aluiziotomazelli/smart-farm-solar-sensor/docs/kicad/solar-sensor.kicad_sch

## KiCad design docs/kicad/solar-sensor.kicad_sch (2026-08-28)

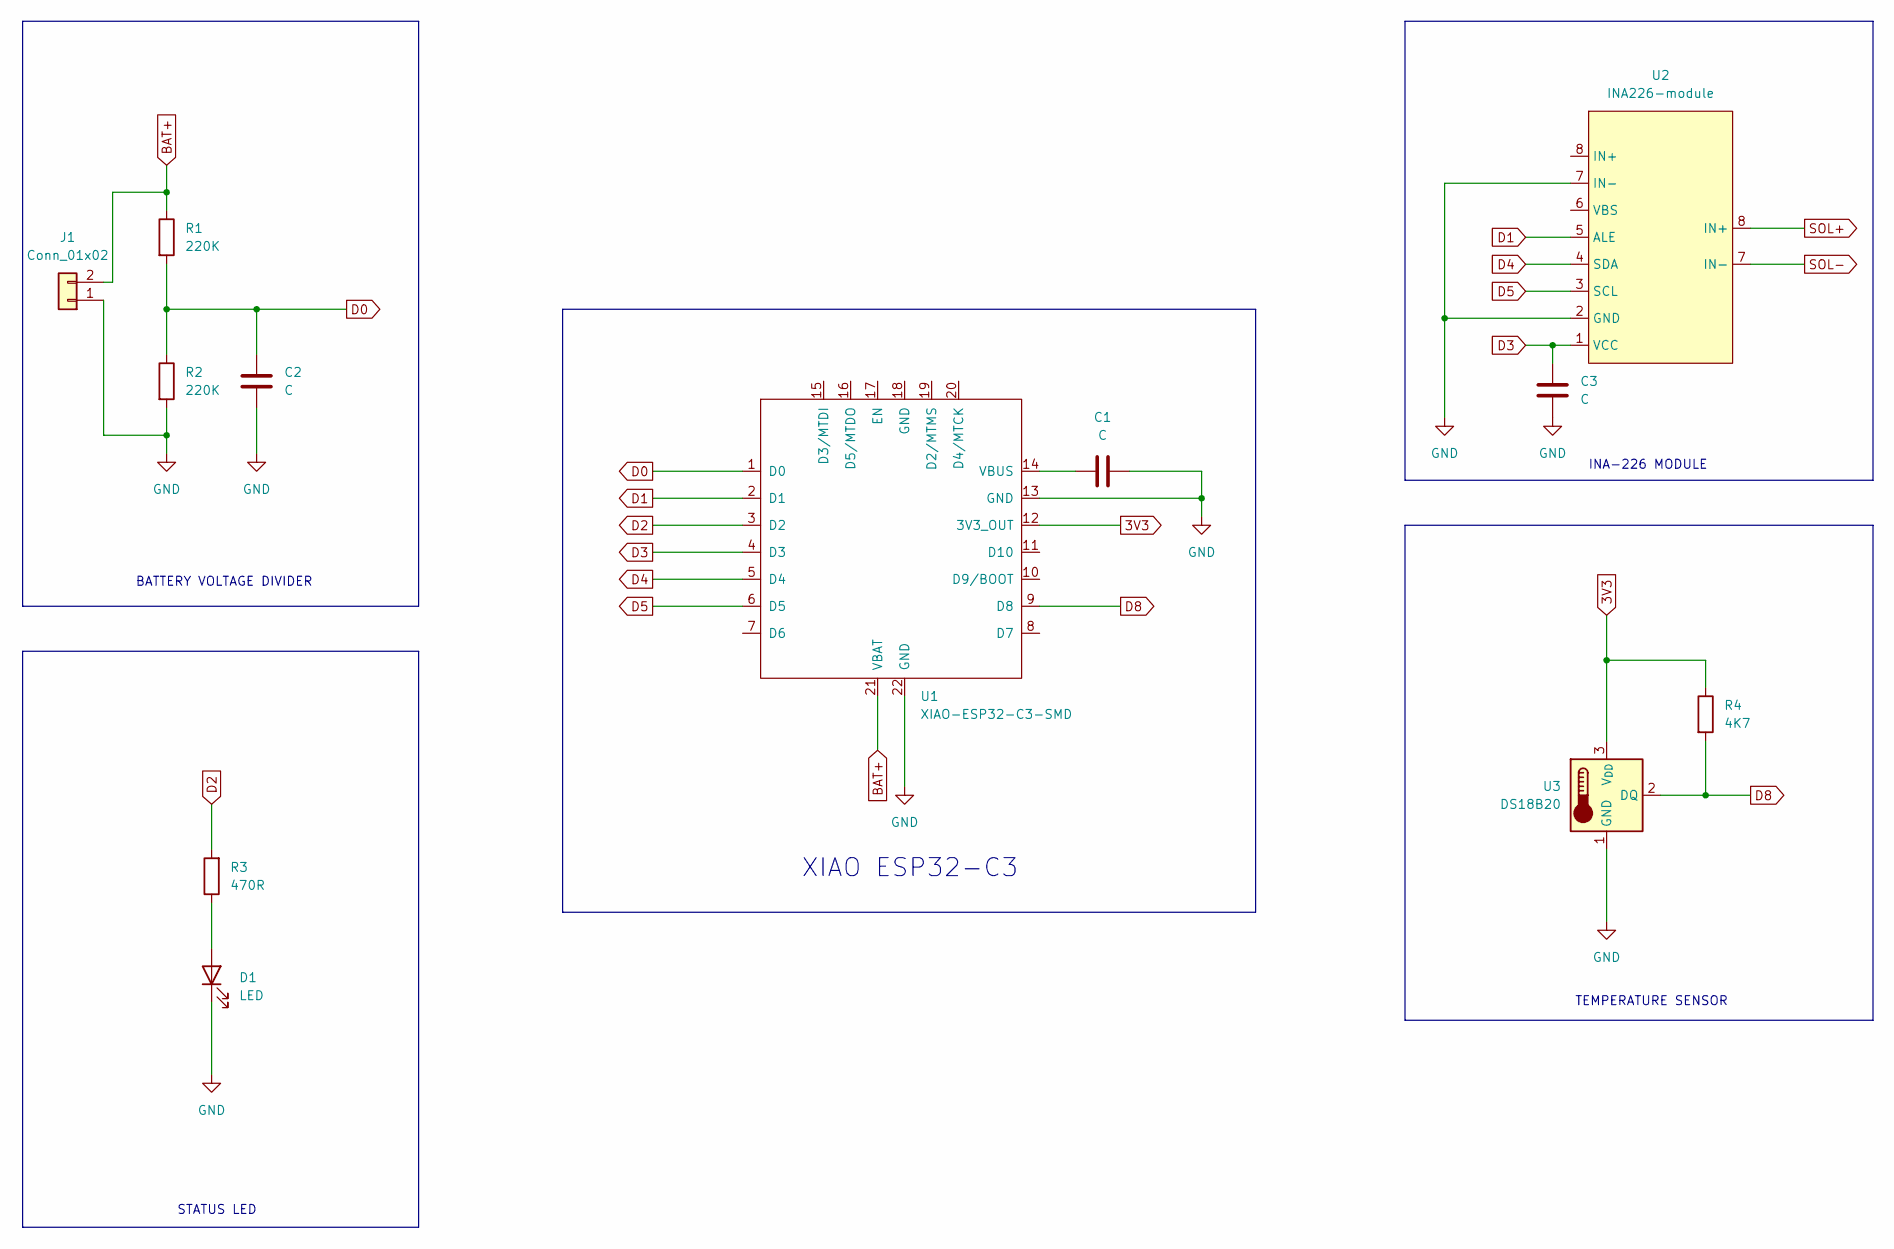
[picture p2: schematic solar-sensor.kicad_sch]

Parts:
C1, C2, C3: C; C_1206_3216Metric_Pad1.33x1.80mm_HandSolder
D1: LED; JST_EH_B2B-EH-A_1x02_P2.50mm_Vertical
J1: Conn_01x02; JST_EH_B2B-EH-A_1x02_P2.50mm_Vertical
R1, R2: 220K; R_1206_3216Metric_Pad1.30x1.75mm_HandSolder
R3: 470R; R_1206_3216Metric_Pad1.30x1.75mm_HandSolder
R4: 4K7; R_1206_3216Metric_Pad1.30x1.75mm_HandSolder
U1: XIAO-ESP32-C3-SMD
U2: INA226-module; PinSocket_1x08_P2.54mm_Vertical
U3: DS18B20; JST_EH_B3B-EH-A_1x03_P2.50mm_Vertical

Connections:
3V3: R4.1, U1.12 (3V3_OUT), U3.3 (V_{DD})
BAT+: J1.2, R1.1, U1.21 (VBAT)
D0: C2.2, R1.2, R2.1, U1.1 (D0)
D1: U1.2 (D1), U2.5 (ALE)
D2: R3.2, U1.3 (D2)
D3: C3.2, U1.4 (D3), U2.1 (VCC)
D4: U1.5 (D4), U2.4 (SDA)
D5: U1.6 (D5), U2.3 (SCL)
D8: R4.2, U1.9 (D8), U3.2 (DQ)
GND: C1.2, C2.1, C3.1, D1.1 (K), J1.1, R2.2, U1.13 (GND), U1.22 (GND), U2.2 (GND), U2.7 (IN-), U3.1 (GND)
unnamed: C1.1, U1.14 (VBUS)
unnamed: D1.2 (A), R3.1
SOL+: U2.8 (IN+)
SOL-: U2.7 (IN-)

Notes on the sheet:
BATTERY VOLTAGE DIVIDER
INA-226 MODULE
TEMPERATURE SENSOR
STATUS LED
XIAO ESP32-C3
