aluiziotomazelli/smart-farm-solar-sensor/host_test/test_solar_sensor/main/test_solar_sensor.cpp

#include <gtest/gtest.h>
#include <gmock/gmock.h>
#include <memory>

#include "solar_sensor.hpp"
#include "mock_ina_sensor_task.hpp"
#include "mock_slow_sensors_task.hpp"
#include "mocks/mock_espnow_manager.hpp"
#include "mock_time_manager.hpp"
#include "mock_persistence_backend.hpp"
#include "nvs_core.hpp"
#include "solar_sensor_nvs.hpp"

#include "mock_hal_timer.hpp"
#include "mock_hal_sleep.hpp"
#include "mock_hal_system.hpp"
#include "mock_hal_freertos.hpp"
#include "mock_hal_gpio.hpp"
#include "mock_hal_i2c.hpp"
#include "mock_ota_controller.hpp"
#include "mock_led_controller.hpp"
#include "mocks/mock_i_wifi_manager.hpp"
#include "mock_day_night_controller.hpp"
#include "mock_command_handler.hpp"

using ::testing::_;
using ::testing::DoAll;
using ::testing::NiceMock;
using ::testing::Return;
using ::testing::SetArgReferee;

class MockOtaTrigger : public IOtaTrigger
{
public:
    MOCK_METHOD(esp_err_t, arm, (IOtaTriggerListener& listener), (override));
    MOCK_METHOD(void, disarm, (), (override));
    MOCK_METHOD(void, notify, (), (override));
};

class SolarSensorTest : public ::testing::Test
{
protected:
    NiceMock<ina::MockInaSensorTask> mock_ina_task_;
    QueueHandle_t dummy_queue_ = reinterpret_cast<QueueHandle_t>(0x5678);
    TelemetrySnapshot snapshot_;
    NiceMock<MockSlowSensorsTask> mock_slow_sensors_task_;

    NiceMock<MockPersistenceBackend> rtc_core_backend_;
    NiceMock<MockPersistenceBackend> nvs_core_backend_;
    NvsCore core_storage_{rtc_core_backend_, nvs_core_backend_};

    NiceMock<MockPersistenceBackend> rtc_solar_backend_;
    NiceMock<MockPersistenceBackend> nvs_solar_backend_;
    SolarSensorNvs solar_storage_{rtc_solar_backend_, nvs_solar_backend_};

    NiceMock<idf_hals::MockTimerHAL> hal_timer_;
    NiceMock<MockOtaController> ota_controller_;
    NiceMock<MockOtaTrigger> btn_trigger_;
    NiceMock<espnow::MockEspNowManager> espnow_;
    QueueHandle_t rx_queue_ = reinterpret_cast<QueueHandle_t>(0x9999);
    NiceMock<wifi_manager::MockWiFiManager> wifi_;
    NiceMock<idf_hals::MockSleepHAL> hal_sleep_;
    NiceMock<idf_hals::MockSystemHAL> hal_system_;
    NiceMock<time_manager::MockTimeManager> time_manager_;
    NiceMock<idf_hals::MockHalFreertos> hal_rtos_;
    NiceMock<idf_hals::MockGpioHAL> hal_gpio_;
    NiceMock<idf_hals::MockI2cHAL> hal_i2c_;
    NiceMock<MockLedController> led_;
    NiceMock<MockDayNightController> day_night_;
    NiceMock<MockCommandHandler> command_handler_;

    class TestableSolarSensor : public SolarSensor
    {
    public:
        using SolarSensor::SolarSensor;
        using SolarSensor::ensure_communication_ready;
    };

    std::unique_ptr<TestableSolarSensor> sut_;

    uint64_t fake_time_us_ = 1000ULL;

    void SetUp() override
    {
        fake_time_us_ = 1000ULL;
        rtc_core_backend_.UseRealStorage();
        nvs_core_backend_.UseRealStorage();
        rtc_solar_backend_.UseRealStorage();
        nvs_solar_backend_.UseRealStorage();

        ON_CALL(hal_timer_, get_time_us()).WillByDefault(::testing::Invoke([this]() {
            uint64_t ret = fake_time_us_;
            fake_time_us_ += 50000ULL; // Advance 50ms per call
            return ret;
        }));

        ON_CALL(hal_rtos_, queue_receive(rx_queue_, _, _)).WillByDefault(Return(pdFALSE));
        ON_CALL(hal_rtos_, queue_receive(dummy_queue_, _, _)).WillByDefault(Return(pdFALSE));
        ON_CALL(mock_slow_sensors_task_, init()).WillByDefault(Return(ESP_OK));
        ON_CALL(mock_slow_sensors_task_, start()).WillByDefault(Return(ESP_OK));
        ON_CALL(mock_ina_task_, is_sampling_enabled()).WillByDefault(Return(true));
        ON_CALL(mock_ina_task_, is_reporting_enabled()).WillByDefault(Return(true));
        ON_CALL(mock_ina_task_, init(_, _)).WillByDefault(Return(ESP_OK));
        ON_CALL(ota_controller_, init(_)).WillByDefault(Return(true));
        ON_CALL(ota_controller_, check_pending_verify()).WillByDefault(Return(false));
        ON_CALL(ota_controller_, confirm_firmware(_)).WillByDefault(Return(OtaActionResult{.success = true}));
        ON_CALL(wifi_, init(_)).WillByDefault(Return(ESP_OK));
        ON_CALL(wifi_, start(_)).WillByDefault(Return(ESP_OK));
        ON_CALL(wifi_, add_credentials(_, _)).WillByDefault(Return(ESP_OK));
        ON_CALL(time_manager_, init(_)).WillByDefault(Return(ESP_OK));
        ON_CALL(espnow_, init(_)).WillByDefault(Return(ESP_OK));
        ON_CALL(espnow_, get_node_state()).WillByDefault(Return(espnow::NodeState::OPERATIONAL));
        ON_CALL(hal_gpio_, config(_)).WillByDefault(Return(ESP_OK));
        ON_CALL(hal_gpio_, isr_handler_add(_, _, _)).WillByDefault(Return(ESP_OK));
        ON_CALL(led_, init()).WillByDefault(Return(ESP_OK));
        ON_CALL(led_, start()).WillByDefault(Return(ESP_OK));
        ON_CALL(day_night_, should_enter_night_mode(_, _)).WillByDefault(Return(false));
        ON_CALL(command_handler_, process()).WillByDefault(Return(CommandProcessResult{}));

        sut_ = std::make_unique<TestableSolarSensor>(
            mock_ina_task_,
            dummy_queue_,
            snapshot_,
            mock_slow_sensors_task_,
            core_storage_,
            solar_storage_,
            hal_timer_,
            ota_controller_,
            btn_trigger_,
            espnow_,
            rx_queue_,
            wifi_,
            hal_sleep_,
            hal_system_,
            time_manager_,
            hal_rtos_,
            hal_gpio_,
            hal_i2c_,
            led_,
            day_night_,
            command_handler_);
    }
};

TEST_F(SolarSensorTest, InitInitializesAndStartsSlowSensorsTask)
{
    EXPECT_CALL(mock_slow_sensors_task_, init()).WillOnce(Return(ESP_OK));
    EXPECT_CALL(mock_slow_sensors_task_, start()).WillOnce(Return(ESP_OK));

    EXPECT_EQ(sut_->init(), ESP_OK);
}

TEST_F(SolarSensorTest, RunProcessesOtaTriggerWhenSet)
{
    sut_->on_ota_triggered(OtaTriggerSource::BUTTON);

    InaSample sample{};
    sample.isc_current_ma = 100;
    sample.status = ESP_OK;

    EXPECT_CALL(hal_rtos_, queue_receive(rx_queue_, _, _))
        .WillRepeatedly(Return(pdFALSE));

    EXPECT_CALL(hal_rtos_, queue_receive(dummy_queue_, _, _))
        .WillOnce(::testing::Invoke([sample](QueueHandle_t, void* data, TickType_t) {
            if (data) {
                *reinterpret_cast<InaSample*>(data) = sample;
            }
            return pdTRUE;
        }))
        .WillRepeatedly(Return(pdFALSE));

    EXPECT_CALL(btn_trigger_, disarm()).Times(1);
    EXPECT_CALL(mock_ina_task_, stop()).Times(1);

    EXPECT_TRUE(sut_->run());
}

TEST_F(SolarSensorTest, RunProcessesInaSamplesAndEntersNightSleepOnDusk)
{
    InaSample sample{};
    sample.isc_current_ma = 0;
    sample.status = ESP_OK;

    EXPECT_CALL(day_night_, should_enter_night_mode(0, _)).WillOnce(Return(true));
    EXPECT_CALL(day_night_, calculate_night_sleep_time_us(_)).WillOnce(Return(3600000000ULL));

    EXPECT_CALL(hal_rtos_, queue_receive(rx_queue_, _, _))
        .WillRepeatedly(Return(pdFALSE));

    EXPECT_CALL(hal_rtos_, queue_receive(dummy_queue_, _, _))
        .WillOnce(::testing::Invoke([sample](QueueHandle_t, void* data, TickType_t) {
            if (data) {
                *reinterpret_cast<InaSample*>(data) = sample;
            }
            return pdTRUE;
        }))
        .WillRepeatedly(Return(pdFALSE));

    EXPECT_CALL(mock_ina_task_, prepare_for_sleep()).WillOnce(Return(ESP_OK));
    EXPECT_CALL(hal_sleep_, enable_timer_wakeup(_)).WillOnce(Return(ESP_OK));
    EXPECT_CALL(hal_sleep_, deep_sleep_enable_gpio_wakeup(_, _)).WillOnce(Return(ESP_OK));
    EXPECT_CALL(hal_sleep_, deep_sleep_start()).Times(1);

    EXPECT_FALSE(sut_->run());

    TelemetrySnapshotData snap = snapshot_.get();
    EXPECT_TRUE(snap.is_night_mode);
}

TEST_F(SolarSensorTest, ProcessInaSampleUpdatesMaxDayCurrentAndAccumulatesYield)
{
    InaSample sample{};
    sample.isc_current_ma = 1000;
    sample.status = ESP_OK;

    EXPECT_CALL(mock_ina_task_, get_expected_sample_period_ms()).WillRepeatedly(Return(3600000u));

    EXPECT_CALL(hal_rtos_, queue_receive(rx_queue_, _, _))
        .WillRepeatedly(Return(pdFALSE));

    EXPECT_CALL(hal_rtos_, queue_receive(dummy_queue_, _, _))
        .WillOnce(::testing::Invoke([sample](QueueHandle_t, void* data, TickType_t) {
            if (data) {
                *reinterpret_cast<InaSample*>(data) = sample;
            }
            return pdTRUE;
        }))
        .WillRepeatedly(Return(pdFALSE));

    EXPECT_TRUE(sut_->run());

    TelemetrySnapshotData snap = snapshot_.get();
    EXPECT_EQ(snap.max_current_ma, 1000);
    EXPECT_EQ(snap.daily_yield_mah, 1000);
}

TEST_F(SolarSensorTest, ProcessNightCalibrationRejectsLightningSpikesAndAppliesMedian)
{
    EXPECT_CALL(hal_rtos_, queue_receive(rx_queue_, _, _)).WillRepeatedly(Return(pdFALSE));

    // Setup 10 samples: 1 initial sample consumed by evaluate_boot_mode(), followed by 9 calibration samples
    // (7 valid zero-offset samples near 0uV, and 2 lightning spikes +500uV and +1500uV)
    std::vector<int32_t> raw_samples = {0, -10, 5, 500, 2, -2, 1500, 8, 0, -4};
    size_t sample_idx = 0;

    EXPECT_CALL(hal_rtos_, queue_receive(dummy_queue_, _, _))
        .WillRepeatedly(::testing::Invoke([&raw_samples, &sample_idx](QueueHandle_t, void* data, TickType_t) {
            if (data && sample_idx < raw_samples.size()) {
                InaSample s{};
                s.shunt_voltage_uv = raw_samples[sample_idx++];
                s.status = ESP_OK;
                *reinterpret_cast<InaSample*>(data) = s;
                return pdTRUE;
            }
            return pdFALSE;
        }));

    EXPECT_CALL(hal_sleep_, get_wakeup_cause()).WillRepeatedly(Return(ESP_SLEEP_WAKEUP_TIMER));
    EXPECT_CALL(time_manager_, is_synchronized()).WillRepeatedly(Return(true));
    EXPECT_CALL(time_manager_, get_timestamp_sec()).WillRepeatedly(Return(10800)); // 03:00 AM UTC
    EXPECT_CALL(day_night_, classify_wake(false, 0, _)).WillOnce(Return(WakeType::CALIBRATION_TIMER));
    EXPECT_CALL(day_night_, calculate_night_sleep_time_us(_)).WillOnce(Return(3600000000ULL));

    EXPECT_CALL(mock_ina_task_, prepare_for_sleep()).WillOnce(Return(ESP_OK));
    EXPECT_CALL(hal_sleep_, enable_timer_wakeup(_)).WillOnce(Return(ESP_OK));
    EXPECT_CALL(hal_sleep_, deep_sleep_enable_gpio_wakeup(_, _)).WillOnce(Return(ESP_OK));
    EXPECT_CALL(hal_sleep_, deep_sleep_start()).Times(1);

    EXPECT_FALSE(sut_->run());

    // Sorted valid calibration samples (ignoring >100uV spikes 500uV and 1500uV): [-10, -4, -2, 0, 2, 5, 8]
    // Median of 7 valid samples (index 7/2 = 3) is 0 uV!
    EXPECT_EQ(sut_->get_solar_stats().shunt_zero_offset_uv, 0);
}

TEST_F(SolarSensorTest, InitSuccessSetsBootSuccessLedPattern)
{
    EXPECT_CALL(led_, init()).WillOnce(Return(ESP_OK));
    EXPECT_CALL(led_, start()).WillOnce(Return(ESP_OK));
    EXPECT_CALL(led_, set_pattern(BlinkPattern::BOOT_SUCCESS)).Times(1);

    EXPECT_EQ(sut_->init(), ESP_OK);
}

TEST_F(SolarSensorTest, InitFailureSetsErrorBurstLedPattern)
{
    EXPECT_CALL(wifi_, init(_)).WillOnce(Return(ESP_FAIL));
    EXPECT_CALL(led_, set_pattern(BlinkPattern::ERROR_BURST)).Times(1);

    EXPECT_EQ(sut_->init(), ESP_FAIL);
}

TEST_F(SolarSensorTest, RunDispatchesRebootCommandFromHandler)
{
    EXPECT_CALL(command_handler_, process())
        .WillOnce(Return(CommandProcessResult{.reboot_requested = true}));
    EXPECT_CALL(wifi_, disconnect(_)).Times(1);
    EXPECT_CALL(espnow_, deinit()).Times(1);
    EXPECT_CALL(hal_system_, restart()).Times(1);

    EXPECT_FALSE(sut_->run());
}

TEST_F(SolarSensorTest, RunDispatchesTimeSyncedCommandFromHandler)
{
    InaSample sample{};
    sample.isc_current_ma = 100;
    sample.status = ESP_OK;

    EXPECT_CALL(command_handler_, process())
        .WillOnce(Return(CommandProcessResult{.time_synced = true}));
    EXPECT_CALL(time_manager_, is_synchronized()).WillRepeatedly(Return(true));
    EXPECT_CALL(time_manager_, get_timestamp_ms()).WillRepeatedly(Return(1767225600000ULL));

    EXPECT_CALL(hal_rtos_, queue_receive(dummy_queue_, _, _))
        .WillOnce(::testing::Invoke([sample](QueueHandle_t, void* data, TickType_t) {
            if (data) {
                *reinterpret_cast<InaSample*>(data) = sample;
            }
            return pdTRUE;
        }))
        .WillRepeatedly(Return(pdFALSE));

    EXPECT_TRUE(sut_->run());
}

TEST_F(SolarSensorTest, EnsureCommunicationReady_ReturnsTrueIfOperational)
{
    EXPECT_CALL(hal_rtos_, task_delay(pdMS_TO_TICKS(100))).Times(1);
    EXPECT_CALL(espnow_, get_node_state()).WillOnce(Return(espnow::NodeState::OPERATIONAL));

    EXPECT_TRUE(sut_->ensure_communication_ready(3));
}

TEST_F(SolarSensorTest, EnsureCommunicationReady_RecoversFromIdleAndReturnsTrue)
{
    EXPECT_CALL(espnow_, get_node_state())
        .WillOnce(Return(espnow::NodeState::IDLE))
        .WillOnce(Return(espnow::NodeState::RECOVERY_SCAN))
        .WillOnce(Return(espnow::NodeState::OPERATIONAL));

    EXPECT_CALL(espnow_, reconnect()).WillOnce(Return(ESP_OK));
    EXPECT_CALL(hal_rtos_, task_delay(pdMS_TO_TICKS(100))).Times(1);
    EXPECT_CALL(hal_rtos_, task_delay(pdMS_TO_TICKS(30))).Times(2);

    EXPECT_TRUE(sut_->ensure_communication_ready(3));
}

TEST_F(SolarSensorTest, EnsureCommunicationReady_WaitsAndReturnsFalseIfAllAttemptsFail)
{
    EXPECT_CALL(espnow_, get_node_state()).WillRepeatedly(Return(espnow::NodeState::RECOVERY_SCAN));
    EXPECT_CALL(hal_rtos_, task_delay(pdMS_TO_TICKS(100))).Times(1);
    EXPECT_CALL(hal_rtos_, task_delay(pdMS_TO_TICKS(30))).Times(testing::AtLeast(1));

    EXPECT_FALSE(sut_->ensure_communication_ready(2));
}

TEST_F(SolarSensorTest, RunProcessesInaSamplesAndRetriesNightReportIfFirstAttemptFails)
{
    InaSample sample{};
    sample.isc_current_ma = 0;
    sample.status = ESP_OK;

    EXPECT_CALL(day_night_, should_enter_night_mode(0, _)).WillOnce(Return(true));
    EXPECT_CALL(day_night_, calculate_night_sleep_time_us(_)).WillOnce(Return(3600000000ULL));

    EXPECT_CALL(hal_rtos_, queue_receive(rx_queue_, _, _))
        .WillRepeatedly(Return(pdFALSE));

    EXPECT_CALL(hal_rtos_, queue_receive(dummy_queue_, _, _))
        .WillOnce(::testing::Invoke([sample](QueueHandle_t, void* data, TickType_t) {
            if (data) {
                *reinterpret_cast<InaSample*>(data) = sample;
            }
            return pdTRUE;
        }))
        .WillRepeatedly(Return(pdFALSE));

    EXPECT_CALL(espnow_, send_data(espnow::ReservedIds::HUB, static_cast<uint8_t>(farm::PayloadType::SOLAR_SENSOR_REPORT), _, _, true))
        .WillOnce(Return(ESP_FAIL))
        .WillOnce(Return(ESP_OK));

    EXPECT_CALL(led_, set_pattern(BlinkPattern::ERROR_BURST)).Times(1);
    EXPECT_CALL(led_, set_pattern(BlinkPattern::ENTER_SLEEP)).Times(1);
    EXPECT_CALL(espnow_, get_node_state()).WillRepeatedly(Return(espnow::NodeState::OPERATIONAL));

    EXPECT_CALL(mock_ina_task_, prepare_for_sleep()).WillOnce(Return(ESP_OK));
    EXPECT_CALL(hal_sleep_, enable_timer_wakeup(_)).WillOnce(Return(ESP_OK));
    EXPECT_CALL(hal_sleep_, deep_sleep_enable_gpio_wakeup(_, _)).WillOnce(Return(ESP_OK));
    EXPECT_CALL(hal_sleep_, deep_sleep_start()).Times(1);

    EXPECT_FALSE(sut_->run());
}
